capuanomat/Mini-Quanser-Project/HARDWARE/Mini Quanser 1.3/Solifwork Files - Grabcad.com/SMALL MOTOR/Renderings/01.jpg

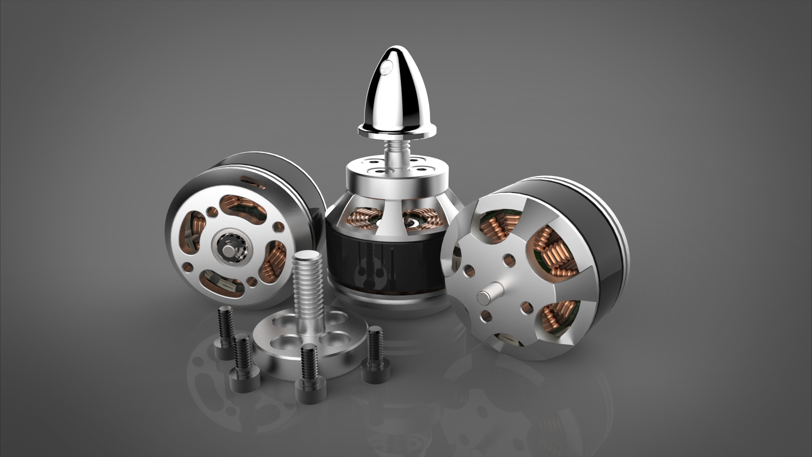
HARDWARE/Mini Quanser 1.3/Solifwork Files - Grabcad.com/SMALL MOTOR/Renderings/01.jpg
