capuanomat/Mini-Quanser-Project/HARDWARE/Mini Quanser 1.3/ESC.png

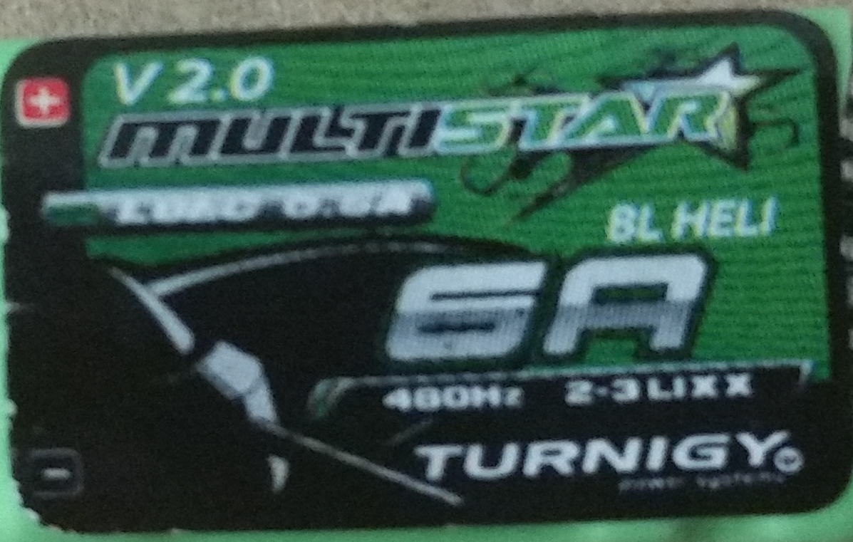
HARDWARE/Mini Quanser 1.3/ESC.png
