capuanomat/Mini-Quanser-Project/HARDWARE/Mini Quanser 1.3/RENDERED.JPG

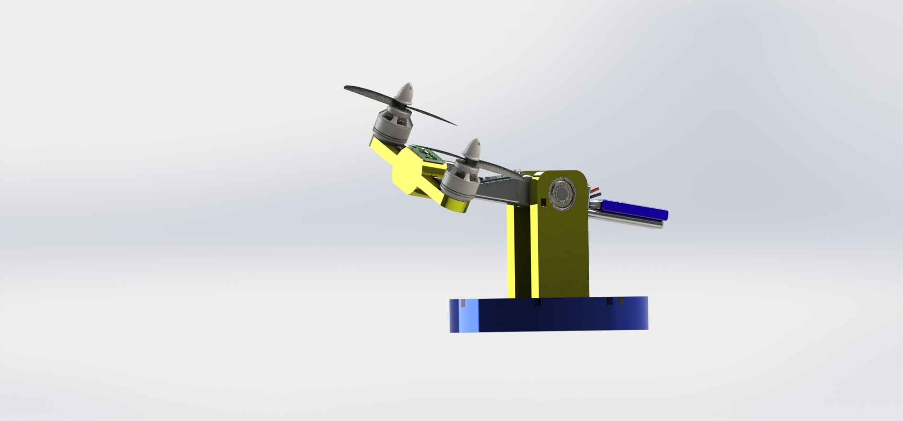
HARDWARE/Mini Quanser 1.3/RENDERED.JPG
