capuanomat/Mini-Quanser-Project/HARDWARE/Mini Quanser 1.3/Solifwork Files - Grabcad.com/MPU6050/MPU Image.png

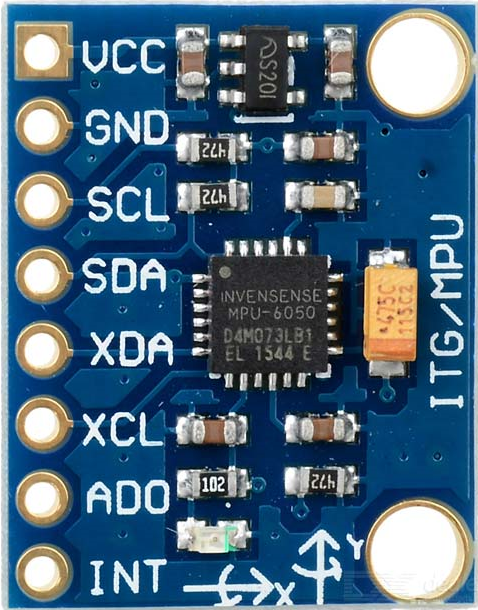
HARDWARE/Mini Quanser 1.3/Solifwork Files - Grabcad.com/MPU6050/MPU Image.png
