capuanomat/Mini-Quanser-Project/HARDWARE/Mini Quanser 1.3/Solifwork Files - Grabcad.com/PROP 5040/New folder/5040PropRender.JPG

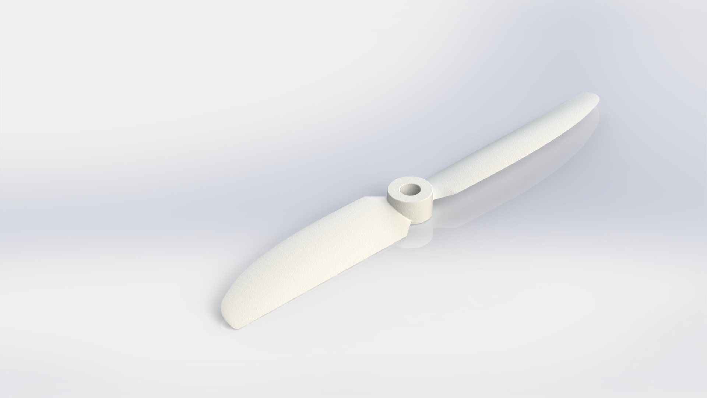
HARDWARE/Mini Quanser 1.3/Solifwork Files - Grabcad.com/PROP 5040/New folder/5040PropRender.JPG
