capuanomat/Mini-Quanser-Project/HARDWARE/Mini Quanser 1.3/Solifwork Files - Grabcad.com/SMALL MOTOR/Product Drawing.JPG

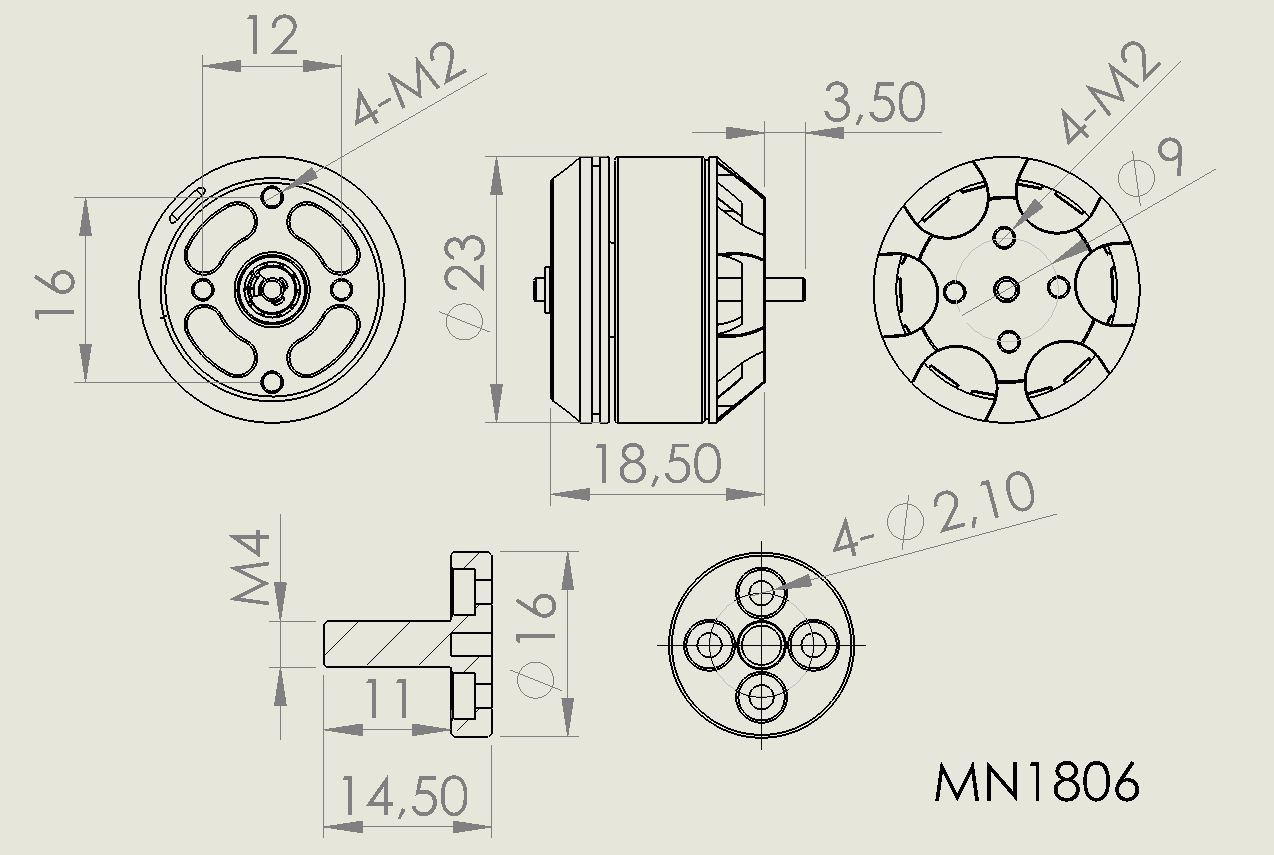
HARDWARE/Mini Quanser 1.3/Solifwork Files - Grabcad.com/SMALL MOTOR/Product Drawing.JPG
