capuanomat/Mini-Quanser-Project/HARDWARE/Mini Quanser 1.3/Zippy 850 Sticker.png

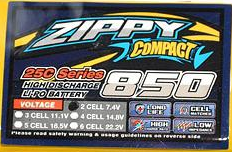
HARDWARE/Mini Quanser 1.3/Zippy 850 Sticker.png
