capuanomat/Mini-Quanser-Project/HARDWARE/Mini Quanser 1.3/Zippy 850.jpg

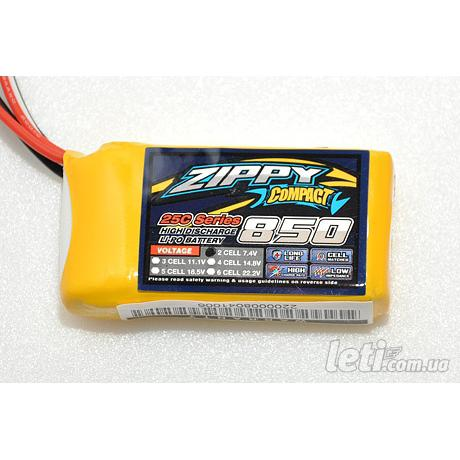
HARDWARE/Mini Quanser 1.3/Zippy 850.jpg
