capuanomat/Mini-Quanser-Project/HARDWARE/Mini Quanser 1.3/Solidwork Files - DESIGN 3/ESC.SLDPRT

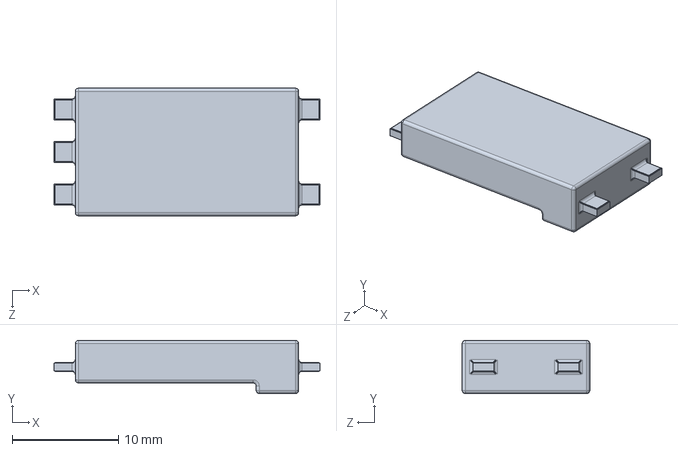
[picture p25: CAD file, 2017-07-20]
HARDWARE/Mini Quanser 1.3/Solidwork Files - DESIGN 3/ESC.SLDPRT
25.0 x 5.00 x 12.0 mm
