capuanomat/Mini-Quanser-Project/HARDWARE/Mini Quanser 1.1/Solidworks Files/Base.SLDPRT

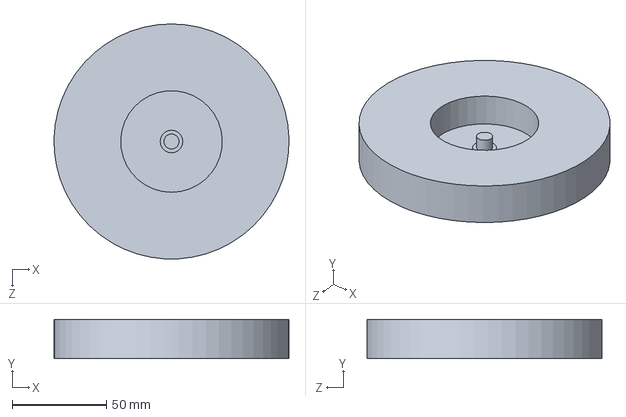
[picture p26: CAD file, 2017-06-29]
HARDWARE/Mini Quanser 1.1/Solidworks Files/Base.SLDPRT
124.9 x 21.0 x 125.0 mm
