capuanomat/Mini-Quanser-Project/HARDWARE/Mini Quanser 1.3/Solidwork Files - DESIGN 1/Counterweight Cover 1.3.SLDPRT

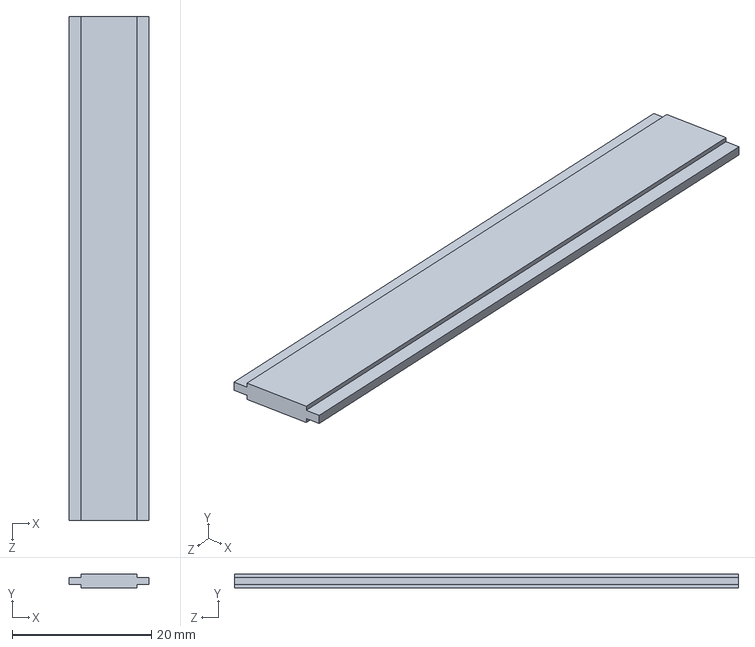
[picture p27: CAD file, 2017-07-07]
HARDWARE/Mini Quanser 1.3/Solidwork Files - DESIGN 1/Counterweight Cover 1.3.SLDPRT
11.5 x 2.00 x 72.5 mm
