capuanomat/Mini-Quanser-Project/HARDWARE/Mini Quanser 1.3/Solidwork Files - DESIGN 2/Motor Mount 1.3 (Two motors).SLDPRT

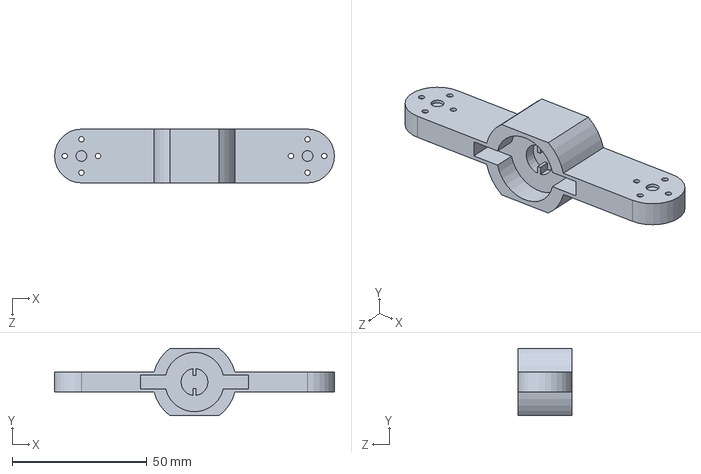
[picture p28: CAD file, 2017-07-13]
HARDWARE/Mini Quanser 1.3/Solidwork Files - DESIGN 2/Motor Mount 1.3 (Two motors).SLDPRT
104.0 x 25.0 x 20.0 mm
