capuanomat/Mini-Quanser-Project/HARDWARE/Mini Quanser 1.3/Solidwork Files - DESIGN 3/Arm Fix.SLDPRT

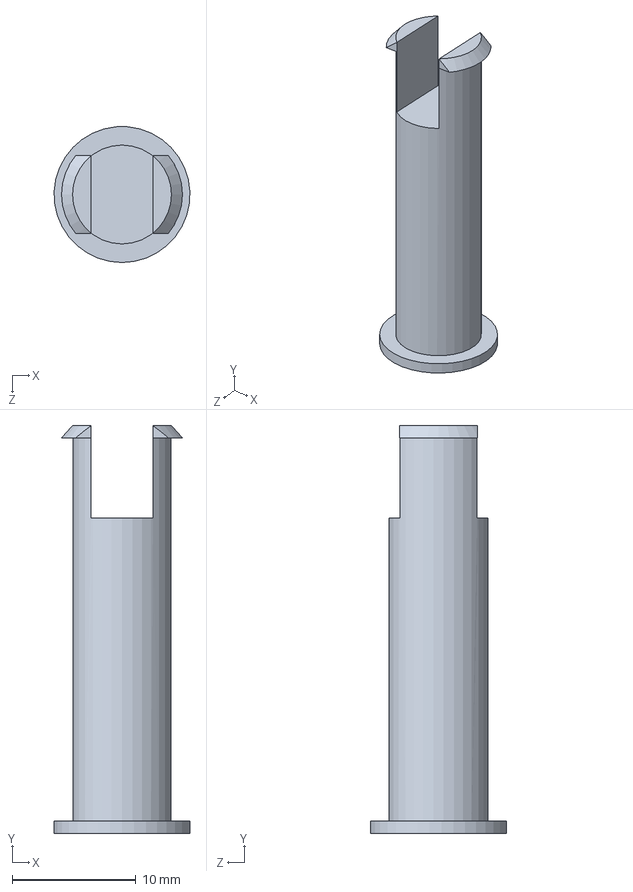
[picture p29: CAD file, 2017-07-20]
HARDWARE/Mini Quanser 1.3/Solidwork Files - DESIGN 3/Arm Fix.SLDPRT
11.0 x 33.0 x 11.0 mm
