capuanomat/Mini-Quanser-Project/HARDWARE/Mini Quanser 1.1/Solidworks Files/Ball Bearings Mount.SLDPRT

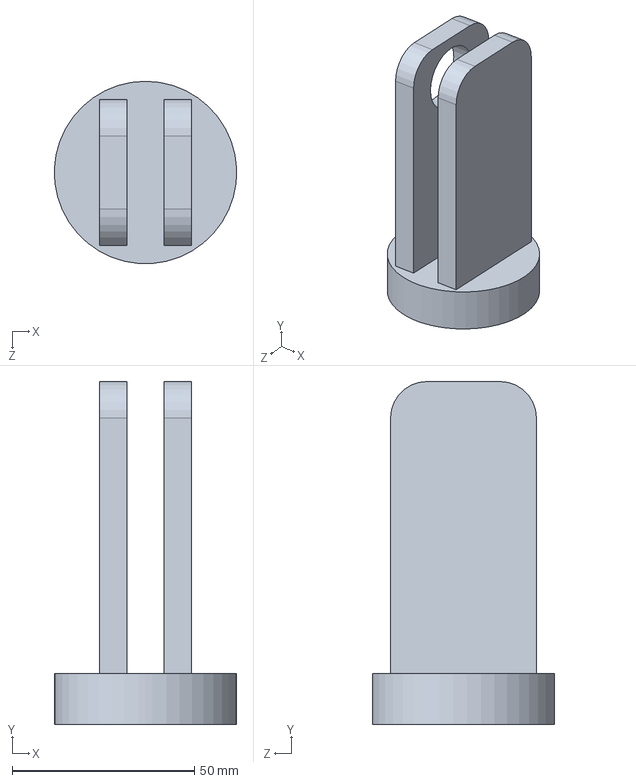
[picture p30: CAD file, 2017-06-29]
HARDWARE/Mini Quanser 1.1/Solidworks Files/Ball Bearings Mount.SLDPRT
50.0 x 94.0 x 50.0 mm
