capuanomat/Mini-Quanser-Project/HARDWARE/Mini Quanser 1.3/Solidwork Files - DESIGN 1/Yaw control 1.3.SLDPRT

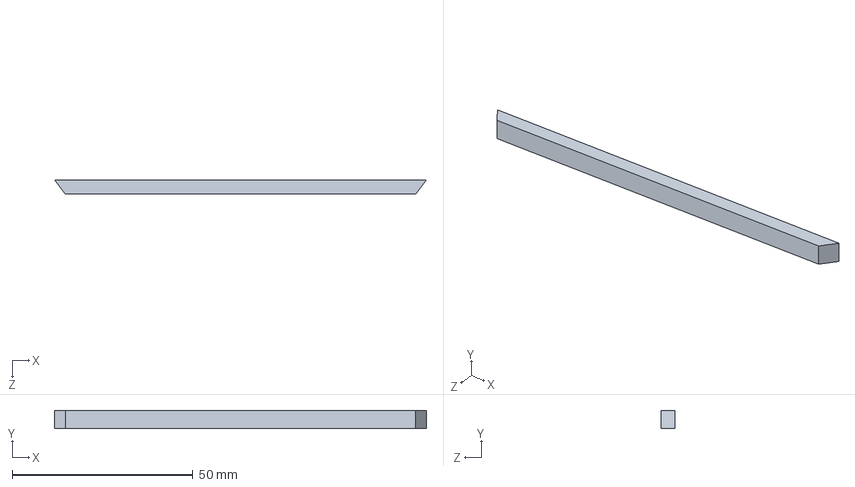
[picture p31: CAD file, 2017-07-07]
HARDWARE/Mini Quanser 1.3/Solidwork Files - DESIGN 1/Yaw control 1.3.SLDPRT
102.9 x 5.00 x 4.00 mm
