capuanomat/Mini-Quanser-Project/HARDWARE/Mini Quanser 1.3/Solidwork Files - DESIGN 2/Motor Arm 1.3.SLDPRT

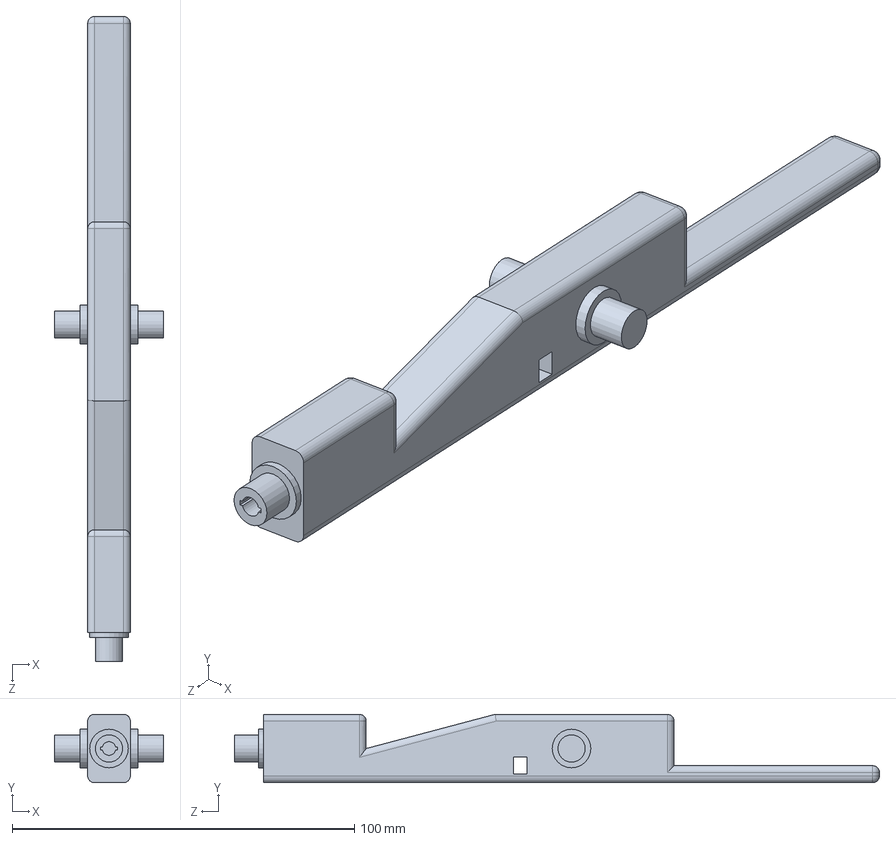
[picture p32: CAD file, 2017-07-13]
HARDWARE/Mini Quanser 1.3/Solidwork Files - DESIGN 2/Motor Arm 1.3.SLDPRT
32.0 x 20.0 x 188.5 mm
