capuanomat/Mini-Quanser-Project/HARDWARE/Mini Quanser 1.3/Solidwork Files - DESIGN 3/Ball Bearings Mount 1.3.SLDPRT

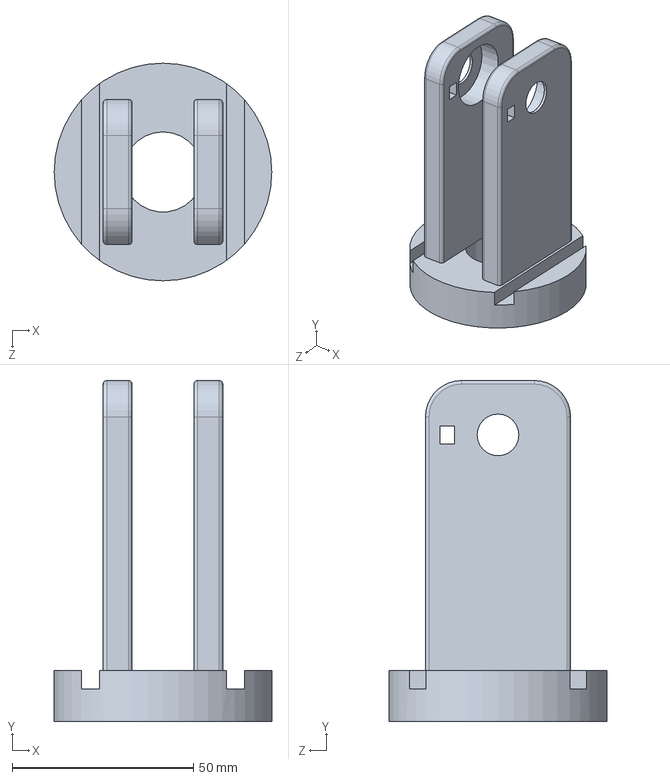
[picture p33: CAD file, 2017-07-20]
HARDWARE/Mini Quanser 1.3/Solidwork Files - DESIGN 3/Ball Bearings Mount 1.3.SLDPRT
60.0 x 94.0 x 60.0 mm
