capuanomat/Mini-Quanser-Project/HARDWARE/Mini Quanser 1.3/Solidwork Files - DESIGN 1/Base 1.3.SLDPRT

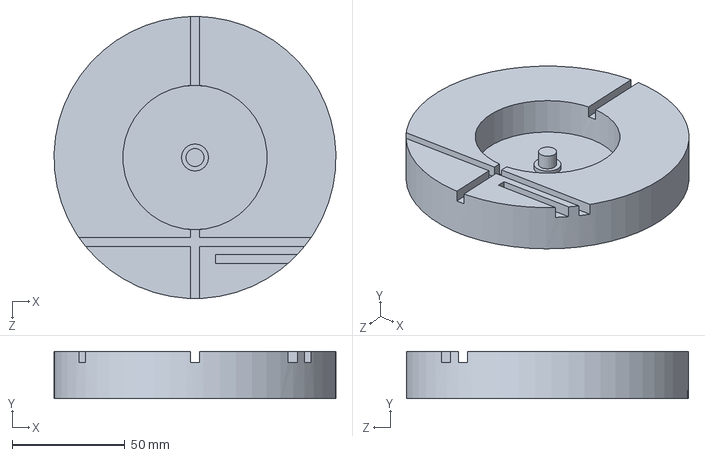
[picture p34: CAD file, 2017-07-07]
HARDWARE/Mini Quanser 1.3/Solidwork Files - DESIGN 1/Base 1.3.SLDPRT
124.9 x 21.0 x 125.0 mm
