capuanomat/Mini-Quanser-Project/HARDWARE/Mini Quanser 1.3/Solidwork Files - DESIGN 2/Base 1.3.SLDPRT

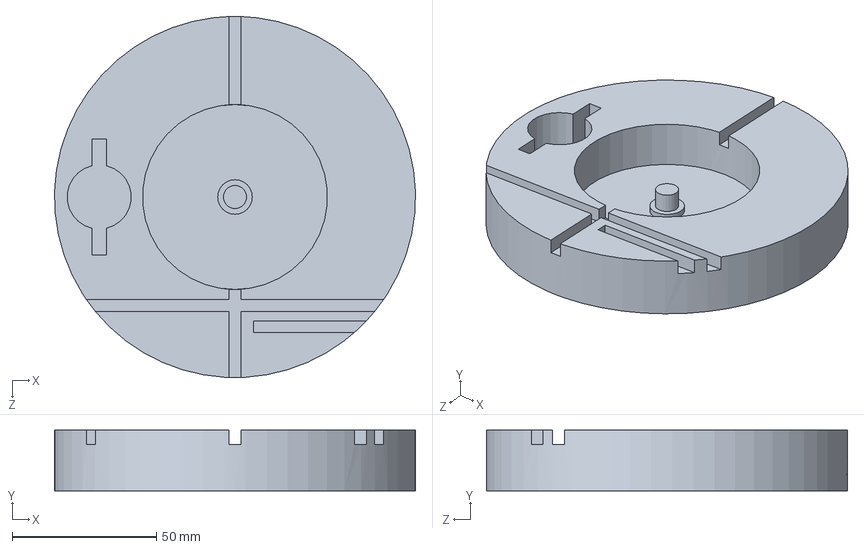
[picture p35: CAD file, 2017-07-13]
HARDWARE/Mini Quanser 1.3/Solidwork Files - DESIGN 2/Base 1.3.SLDPRT
124.9 x 21.0 x 125.0 mm
