capuanomat/Mini-Quanser-Project/HARDWARE/Mini Quanser 1.3/Solidwork Files - DESIGN 3/Motor Mount 1.3 (Two motors).SLDPRT

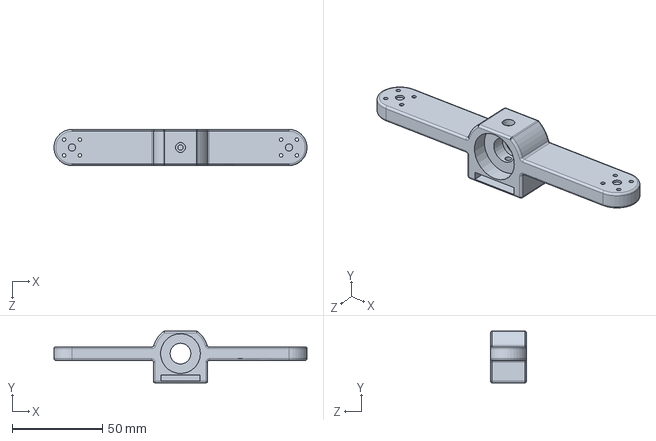
[picture p36: CAD file, 2017-07-20]
HARDWARE/Mini Quanser 1.3/Solidwork Files - DESIGN 3/Motor Mount 1.3 (Two motors).SLDPRT
139.9 x 28.8 x 20.0 mm
