capuanomat/Mini-Quanser-Project/HARDWARE/Mini Quanser 1.3/Solidwork Files - DESIGN 1/Roll Control Piece 1.3.SLDPRT

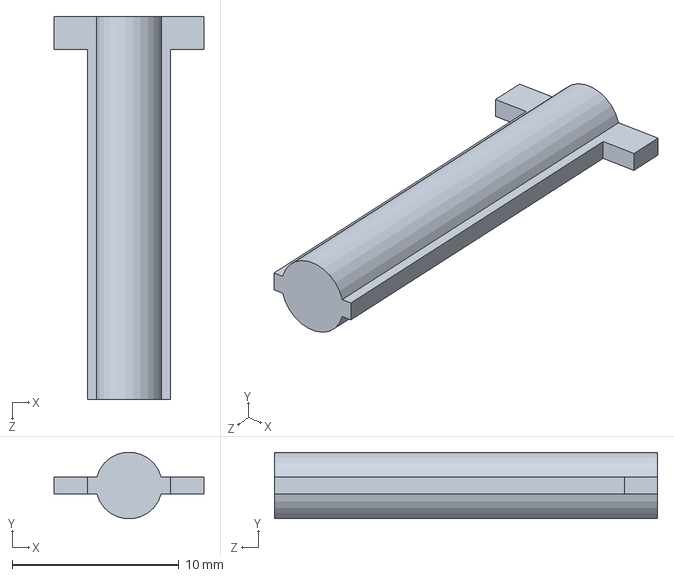
[picture p37: CAD file, 2017-07-07]
HARDWARE/Mini Quanser 1.3/Solidwork Files - DESIGN 1/Roll Control Piece 1.3.SLDPRT
9.00 x 3.97 x 23.0 mm
