capuanomat/Mini-Quanser-Project/HARDWARE/Mini Quanser 1.3/Solidwork Files - DESIGN 3/Base 1.3.SLDPRT

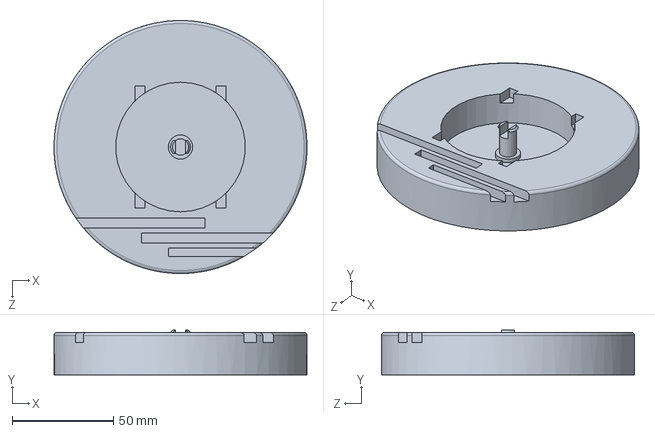
[picture p38: CAD file, 2017-07-20]
HARDWARE/Mini Quanser 1.3/Solidwork Files - DESIGN 3/Base 1.3.SLDPRT
124.9 x 22.0 x 125.0 mm
