capuanomat/Mini-Quanser-Project/HARDWARE/Mini Quanser 1.3/Solidwork Files - DESIGN 3/Pitch Control Piece 1.3.SLDPRT

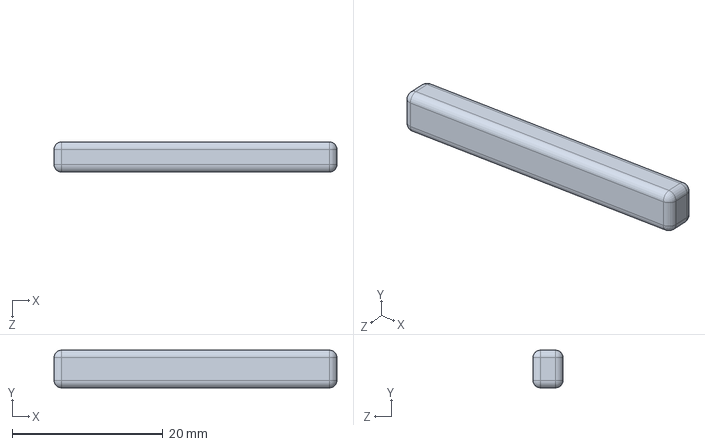
[picture p39: CAD file, 2017-07-20]
HARDWARE/Mini Quanser 1.3/Solidwork Files - DESIGN 3/Pitch Control Piece 1.3.SLDPRT
37.5 x 5.00 x 4.00 mm
