capuanomat/Mini-Quanser-Project/HARDWARE/Mini Quanser 1.3/Solidwork Files - DESIGN 1/Pitch Control Piece 1.3.SLDPRT

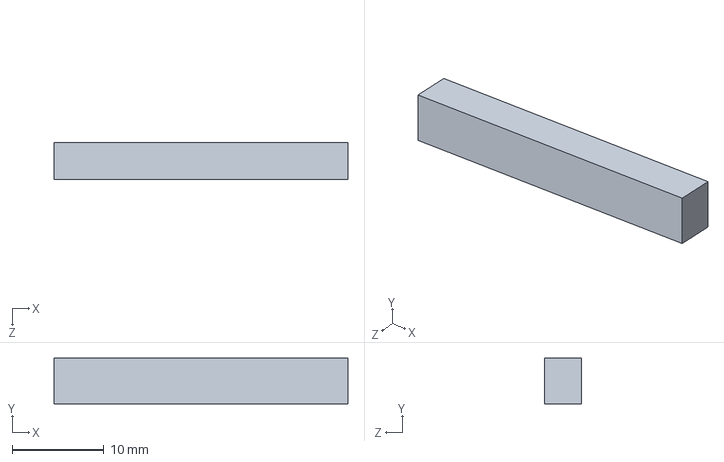
[picture p40: CAD file, 2017-07-07]
HARDWARE/Mini Quanser 1.3/Solidwork Files - DESIGN 1/Pitch Control Piece 1.3.SLDPRT
32.0 x 5.00 x 4.00 mm
