capuanomat/Mini-Quanser-Project/HARDWARE/Mini Quanser 1.3/Solidwork Files - DESIGN 3/Yaw control 1.3.SLDPRT

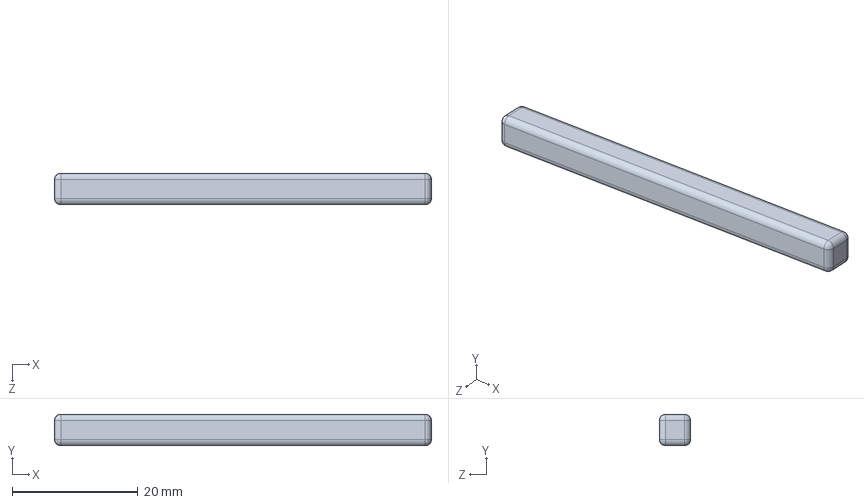
[picture p41: CAD file, 2017-07-20]
HARDWARE/Mini Quanser 1.3/Solidwork Files - DESIGN 3/Yaw control 1.3.SLDPRT
60.0 x 5.00 x 5.00 mm
