capuanomat/Mini-Quanser-Project/HARDWARE/Mini Quanser 1.3/Solidwork Files - DESIGN 3/Zippy 850 Battery.SLDPRT

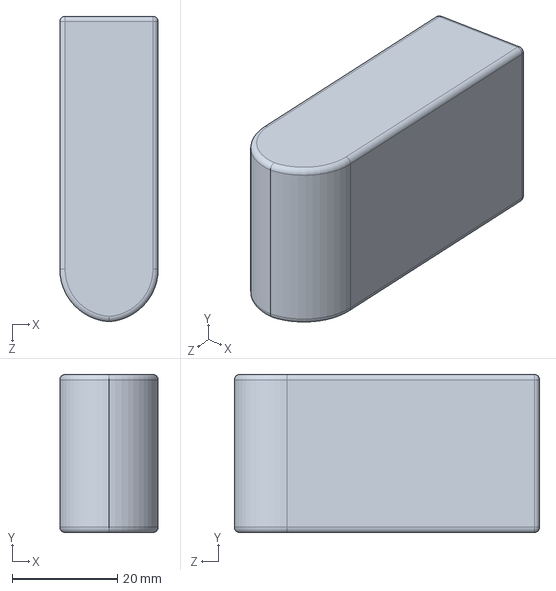
[picture p42: CAD file, 2017-07-16]
HARDWARE/Mini Quanser 1.3/Solidwork Files - DESIGN 3/Zippy 850 Battery.SLDPRT
18.7 x 30.0 x 58.0 mm
